StefanZott/SmartHomeSystemBasisStation/tmp/tasks/done/0047_pcb-layout-stromversorgung-leds.md

---
title: PCB-Layout — Stromversorgung und Status-LEDs platzieren und routen
created: 2026-09-24
jira: SHBS-21
priority: high
type: feature
status: done
---

## Kontext

Stromversorgung und Status-LEDs sind im Schaltplan fertig, im PCB aber erst
teilweise umgesetzt. Das Review vom 2026-09-24
([Report](../../report/2026-09-24_pcb-review-stromversorgung-leds.md))
ergab mehrere Befunde (B2–B5). Ethernet läuft separat unter SHBS-10.

## Ziel

Stromversorgung und LEDs vollständig platziert und geroutet, mit eigener
Netzklasse für die Versorgungsnetze. DRC im Bereich ohne Fehler.

## Schritte

- [x] Erste Platzierung und Routing durch Bediener (WIP-Stand)
- [x] Netzklasse `Power` (0,6 mm, Via 0,8/0,4) für VBUS, +5V, +3V3, GND, SW anlegen (B2)
- [x] Schaltknoten im Schaltplan mit lokalem Label `SW` benennen
- [x] Bediener: KiCad öffnen, im PCB-Editor F8 (Netz `Net-(D11-K)` → `/Stromversorgung/SW`)
- [x] ~~Versorgungsleitungen auf Netzklassenbreite aufweiten~~ → ausgelagert in Task 0048
- [x] Buck-Wandler kompakt um PS1 anordnen, Schaltknoten kurz halten (B3)
- [x] Bediener: PCB öffnen, `B` (Zonen füllen), Sichtprüfung Wandler, speichern
- [x] +3V3 zu U6.2 und zu den LED-Anoden routen (B4)
- [x] Bediener: `B` und speichern nach B4-Routing
- [x] ~~DRC-Restmeldungen an J_PWR1 ausschließen~~ → ausgelagert in Task 0048:: 2× `starved_thermal`
      (A1, rechtes S1), 2× Kantenabstand NPTH (A12, linkes S1) —
      Hersteller-Landepattern, Pads per Leiterbahn angebunden (aus SHBS-20)
- [x] `docs/project/power_supply.md` und `hardware.md` um Layout-Stand ergänzen
- [x] Commit

## Fortschritt

- 2026-09-24: Task angelegt. Bediener hat Stromversorgung und LEDs erstmals
  platziert und geroutet, Zonen gefüllt. DRC gesamt: 75 Meldungen, davon
  144 offene Verbindungen überwiegend außerhalb dieses Bereichs. Stand wird
  als WIP-Commit gesichert, damit SHBS-20 separat committet werden kann.
  Nächster Schritt: Netzklasse `Power` (Punkt 2 des Reviews).

- 2026-09-25: Label `SW` in `Stromversorgung.kicad_sch` auf der Leitung ab
  PS1.6 gesetzt (Netzliste: `/Stromversorgung/SW` = C15.2, D11.1, L1.2,
  PS1.6; ERC unverändert). Netzklasse `Power` mit fünf Mustern in
  `BasisStation.kicad_pro` angelegt. Muster per DRC-Probe in Kopie geprüft
  (Abstand testweise 5 mm): GND, +3V3, VBUS, +5V greifen, SW erst nach F8.
  `power_supply.md` ergänzt. Nächster Schritt: F8 durch Bediener, dann
  Leitungen aufweiten.

- 2026-09-26: Buck-Wandler per Skript in der `.kicad_pcb` umplatziert
  (KiCad geschlossen, Sicherung im Scratchpad). C13 (66/49,3), C15
  (63,3/53,5, 90°), D11 (60,2/50,5, 90°), L1 (60,2/58,8, 90°), C14
  (60,2/64,1, 90°), R17 (67,5/57,5, 90°), R18 (69,5/57,5, 90°). 53 alte
  Leiterbahnen/Vias entfernt (SW, BST, FB, +3V3 komplett, +5V und GND am
  Wandler), neu geroutet auf F.Cu: Power-Netze 0,6 mm, BST 0,3, FB 0,25,
  5 GND-Vias 0,8/0,4. SW-Leitung ca. 9,2 mm (vorher 40,7 mm). Referenztexte
  von PS1, C15, R18 versetzt. DRC per CLI: im Bereich keine Kupfer-,
  Courtyard- oder Silk-Befunde außer veralteter Zonenfüllung; offen nur
  +3V3 zu U6/U7 (B4, bekannt). Nächster Schritt: `B` durch Bediener, dann
  +3V3 verteilen (B4).
- 2026-09-26 (später): Bediener hat Zonen gefüllt und gespeichert. DRC:
  75 Meldungen, davon **keine** im Wandler-Bereich. Kupferbefunde nur noch
  außerhalb: J_PWR1 (bekannte Ausschlüsse), U1-Padabstände, GND-Stummel
  (21,8/90,3). Offen im Bereich nur +3V3 zu U6/U7 (B4).
- 2026-09-26 (B4): +3V3 per Skript geroutet (F.Cu, 0,6 mm). Hauptleitung
  R17-Knick (67,5/62,1) → y 62,1 bis x 111 → 45° → U6.2 (119,35/64,45).
  LED-Zweig ab (105/62,1) über U6 (y 58,1) bis x 150, senkrecht bis
  y 155, Sammelleitung y 157,5 mit Stichen zu D7/D10/D8/D9-Anoden. Erste
  Variante links an U6 vorbei (x 105) wieder verworfen, weil sie USB, EN
  und ETH-SPI auf F.Cu abgeschnitten hätte. DRC: +3V3 außerhalb Ethernet
  vollständig verbunden, Kupferbefunde nur gegen veraltete Zonenfüllung.
- 2026-09-26 (B4, nach `B`): DRC 75 Meldungen (Stand wie vor B4, keine
  neuen), offene Verbindungen 144 → 139. Keine Befunde an den neuen
  +3V3-Leitungen.
- 2026-09-26: Abschluss auf Wunsch des Bedieners. Aufweiten VBUS/+5V und
  DRC-Ausschlüsse J_PWR1 in Task
  [0048](../open/0048_pcb-power-leitungen-aufweiten-drc-ausschluesse.md)
  ausgelagert (gleiches Ticket SHBS-21, bleibt offen). `hardware.md` um
  Layout-Stand ergänzt. Task nach `done/` verschoben.

## Commits

- c2ccc4a (WIP) Erster Layout-Stand Stromversorgung und LEDs
- 53c2221 (WIP) Netzklasse Power, Label SW, Session-Übergabe tmp/memory.md
- 0c19f62 (WIP) Buck-Wandler kompakt um PS1 platziert und neu geroutet
- 895aab9 +3V3 zu U6 und LED-Anoden geroutet, Task abgeschlossen

## Offene Fragen

- Keine.
