StefanZott/SmartHomeSystemBasisStation/tmp/tasks/done/0004_shbs5-rj45-magnetics-schaltplan.md

---
status: done
priority: high
type: feature
created: 2026-09-17
jira: SHBS-5
parent_jira: SHBS-3
---

# RJ45-Buchse, Leitungsterminierung und Link-LEDs im Schaltplan

## Ziel

Buchsenseite der Ethernet-Sektion auf dem Blatt `Ethernet.kicad_sch`
ergänzen: RJ45 mit integrierten Magnetics, Terminierung, Schirmanbindung und
Link-/Activity-LEDs.

Setzt Tasks `0002` und `0003` voraus.

## Aufgaben

1. RJ45-Buchse (Typ aus Task `0002`) platzieren und differenzielle Paare
   `TXP`/`TXN` und `RXP`/`RXN` mit dem W5500 verbinden.
2. **Mittelanzapfungen** der Übertrager gemäss Datenblatt beschalten —
   üblicherweise über je einen Kondensator gegen GND oder gegen eine gefilterte
   Versorgung. Verbindlich ist das Applikationsbeispiel des Buchsen-Datenblatts
   in Kombination mit dem W5500-Referenzdesign.
   **Achtung (WIZnet-Referenz):** Sind die Mittelanzapfungen *innerhalb* des
   Übertragers bzw. der RJ45-Buchse bereits zusammengefasst, muss das
   Anpassnetzwerk der `RX±`-Seite (2 × 50 Ω) **galvanisch vom CT-Knoten
   (3,3 V) getrennt** werden. Vor dem Zeichnen im Datenblatt der gewählten
   Buchse prüfen, ob die CTs intern verbunden sind.
3. **Bob-Smith-Terminierung** auf der Leitungsseite: je 75 Ω von den vier
   ungenutzten Paaren bzw. den Mittelpunkten auf einen gemeinsamen Knoten,
   von dort über einen HV-Kondensator (mind. 2 kV) gegen Chassis-GND.
4. **Schirmanbindung:** Schirm der Buchse auf ein separates `CHASSIS`-Netz.
   Die Verbindung zu Signal-GND als **bestückbare Option** ausführen (0-Ω-Brücke
   plus paralleler HV-Kondensator), damit die Kopplung bei EMV-Problemen
   umkonfiguriert werden kann, ohne die Platine zu ändern.
5. **Link-/Activity-LEDs:** LED-Ausgänge des W5500 sind **active low** und
   treiben gegen GND. Vorwiderstände nach dem Muster der Status-LEDs
   dimensionieren (vgl. `R13`–`R16`, 220 Ω). Prüfen, ob die gewählte Buchse
   die LEDs bereits integriert — dann entfallen diskrete LEDs.
6. Referenzen fortlaufend zur bestehenden Nummerierung vergeben (aktuell
   höchste: `R26`, `D12`, `C15`, `J6`, `U6`).
7. ERC laufen lassen; auf dem `CHASSIS`-Netz ein `PWR_FLAG` setzen, sonst
   meldet KiCad ein nicht getriebenes Netz.

## Sollbeschaltung RJ45 (`T1`, Würth 7499011121A)

Der Bediener zeichnet in KiCad; der Agent prüft danach gegen die Netzliste.

**Die Buchse bringt Bob-Smith-Terminierung und den 2-kV-Kondensator bereits
mit** (4 × 75 Ω + 1 nF/2 kV, Datenblatt S. 2, an den Kabelkontakten 4, 5, 7 und 8 —
nicht zu verwechseln mit Schaltplan-Referenzen).
Extern ist dafür **nichts** zu bauen. Übertrager 1:1, 350 µH — deckt sich mit
der Forderung des W5500-Datenblatts (Abschnitt 5.5.5).

### Signalpaare

| Buchsen-Pin | Signal | Netz |
| --- | --- | ---- |
| 1 | `TD+` | `ETH_TXP` |
| 3 | `TD−` | `ETH_TXN` |
| 4 | `RD+` | `ETH_RXP` |
| 6 | `RD−` | `ETH_RXN` |

> **Fallstrick:** Eine Textextraktion des Datenblatt-Schaltbilds liefert die
> Reihenfolge `RD+, CRD, RD−, TD+, CTD, TD−` — **Sende- und Empfangspaar
> vertauscht**. Die obige Zuordnung wurde über die Koordinaten der
> Beschriftung im PDF geprüft und stimmt mit dem offiziellen Würth-Symbol
> überein.

### Mittelanzapfungen und MDI-Abschluss

Geklärt am 18.09.2026 aus dem WIZnet-Referenzschaltbild
(`pcb/Datasheets/wiznet_W5500_ref-schematic_RJ45-with-magnetics.pdf`).
Vollständiger Abgleich:
[tmp/report/2026-09-18_shbs-5-mdi-referenzabgleich.md](../../report/2026-09-18_shbs-5-mdi-referenzabgleich.md).

Die Sende- und Empfangszweige brauchen mehr als die blosse Paarverbindung.
Der Sendetreiber des W5500 arbeitet stromgesteuert und braucht eine
**gespeiste** Mittelanzapfung; der Empfänger arbeitet spannungsgesteuert,
bringt seine Vorspannung selbst mit und wird deshalb **gleichstromgetrennt**.

**Sendezweig**

| Bauteil | von | nach |
| --- | --- | ---- |
| 49,9 Ω 1 % | `+3V3A` | `U7.1` `TXN` |
| 49,9 Ω 1 % | `+3V3A` | `U7.2` `TXP` |
| 10 Ω 1 % | `+3V3A` | Knoten `TCT` |
| 22 nF | Knoten `TCT` | `GND` |
| — | Knoten `TCT` | `T1.2` `CTD` |

**Empfangszweig**

| Bauteil | von | nach |
| --- | --- | ---- |
| 6,8 nF | `U7.6` `RXP` | `T1.4` `RD+` — **in Serie**, ersetzt die direkte Verbindung |
| 6,8 nF | `U7.5` `RXN` | `T1.6` `RD−` — **in Serie**, ersetzt die direkte Verbindung |
| 49,9 Ω 1 % | `U7.6` `RXP` (chipseitig, vor dem Kondensator) | Knoten `RCT` |
| 49,9 Ω 1 % | `U7.5` `RXN` (chipseitig, vor dem Kondensator) | Knoten `RCT` |
| 10 nF | Knoten `RCT` | `GND` |
| — | Knoten `RCT` | `T1.5` `CRD` |

> **Achtung bei den 6,8 nF:** Sie liegen **in Serie** in den beiden
> Empfangsleitungen. Die bestehende Direktverbindung `U7.6`–`T1.4` und
> `U7.5`–`T1.6` wird dadurch aufgetrennt. Die 49,9 Ω hängen auf der
> **Chipseite** der Kondensatoren.

Warum das nicht optional ist: Ohne die Abschlusswiderstände stimmt die
Leitungsimpedanz nicht, ohne die Serienkondensatoren liegt der Gleichanteil
des Chips auf dem Übertrager. Beides zeigt weder ERC noch ein einfacher
Funktionstest — die Symptome sind sporadische Paketfehler und Abbrüche bei
längeren Kabeln.

### Getrennte Analogversorgung (entschieden 18.09.2026)

Digital- und Analogversorgung werden getrennt, **innerhalb von SHBS-5**.
Begründung: Späteres Nachrüsten hiesse, die sieben Abblockkondensatoren aus
Task 0003 ein zweites Mal umzuhängen. Der Buck-Zweig aus SHBS-4 ist nicht
betroffen — die Ferritperle sitzt auf dem Ethernet-Blatt.

**Neues Netz `+3V3A`**, gespeist aus `+3V3` über eine Ferritperle:

| Bauteil | von | nach | Hinweis |
| --- | --- | ---- | --- |
| Ferritperle `FB1` | `+3V3` | `+3V3A` | 100–2000 Ω bei 100 MHz, Dauerstrom ≥ 300 mA |
| `PWR_FLAG` | `+3V3A` | — | sonst meldet ERC das Netz als nicht getrieben |

**Umzuhängen von `+3V3` auf `+3V3A`:**

| Bisher auf `+3V3` | Neu |
| --- | --- |
| `U7.4`, `U7.8`, `U7.11`, `U7.15`, `U7.17`, `U7.21` (`AVDD`) samt `C17`–`C22` | `+3V3A` |
| `C27` 10 µF Stützkondensator | `+3V3A` |
| Abschlusswiderstände `TXP`/`TXN` (49,9 Ω, siehe oben) | `+3V3A` |
| Speisung `TCT` (10 Ω, siehe oben) | `+3V3A` |

**Bleibt auf `+3V3` (digital):**

| | |
| --- | --- |
| `U7.28` `VDD` samt `C16` | Digitalversorgung des Bausteins |
| `R28`–`R32` | Pull-ups an PMODE, `INTn`, `RSTn` |
| `R33`, `R34` | LED-Vorwiderstände |

Das entspricht der Aufteilung im Referenzschaltbild, wo `3V3D` den `VDD`-Pin
und die LEDs speist, während `3V3A` an allen `AVDD`-Pins und am Sendezweig
liegt.

**Hinweis:** Dieser Schritt ändert Bauteile, die in Task 0003 bereits gesetzt
wurden. Das ist beabsichtigt — Task 0003 bleibt abgeschlossen, die Änderung
läuft unter 0004, weil sie erst durch den Referenzabgleich entstanden ist.

### Schirm und unbenutzte Pins

| Buchsen-Pin | Beschaltung |
| --- | --- |
| `S1`, `S2` | Netz `CHASSIS` |
| 7, 8 | offen lassen, No-Connect-Flag |

Kopplung `CHASSIS` gegen `GND` als **bestückbare Option**: 0-Ω-Brücke parallel
zu einem HV-Kondensator (mind. 2 kV). So lässt sich das Verhalten bei
EMV-Problemen ohne Platinenänderung umkonfigurieren. `PWR_FLAG` auf `CHASSIS`
setzen, sonst meldet ERC ein nicht getriebenes Netz.

### Link- und Activity-LEDs

Die LEDs sitzen in der Buchse. Die LED-Ausgänge des W5500 sind **active low**
und ziehen gegen `GND` — die Anode liegt daher über den Vorwiderstand auf
`+3V3`.

| Buchsen-Pin | Funktion | Beschaltung |
| --- | --- | --- |
| 11 | LED grün, Anode | über **220 Ω** nach `+3V3` |
| 12 | LED grün, Kathode | `ETH_LINKLED` → W5500 Pin 25 |
| 9 | LED gelb, Anode | über **220 Ω** nach `+3V3` |
| 10 | LED gelb, Kathode | `ETH_ACTLED` → W5500 Pin 27 |

Dimensionierung: Flussspannung laut Würth-Datenblatt 1,8–2,4 V bei 20 mA. Bei
3,3 V und 220 Ω stellen sich rund **6 mA** ein — konsistent zu den
Status-LEDs `D7`–`D10` des Projekts, die ebenfalls 220 Ω verwenden.

| Bauart | Bauteil | Wert | Symbol | Footprint | Anzahl | Status |
| --- | --- | ---- | --- | --- | --- | --- |
| **Widerstand** | LED-Vorwiderstand | 220 Ω, 5 % | `Device:R` | `Resistor_SMD:R_0805_2012Metric` | 2 | `R33`, `R34` gesetzt |
| Kondensator | HV-Kopplung `CHASSIS`–`GND` | 1 nF, **≥ 2 kV** | `Device:C` | gehäuseabhängig, 1206 oder größer | 1 | `C28` gesetzt, Typ offen |
| **Widerstand** | Brücke `CHASSIS`–`GND` | 0 Ω, **DNP** | `Device:R` | `Resistor_SMD:R_0805_2012Metric` | 1 | `R35` gesetzt |
| **Widerstand** | Abschluss `TXP`/`TXN` | 49,9 Ω, **1 %** | `Device:R` | `Resistor_SMD:R_0805_2012Metric` | 2 | offen |
| **Widerstand** | Abschluss `RXP`/`RXN` | 49,9 Ω, **1 %** | `Device:R` | `Resistor_SMD:R_0805_2012Metric` | 2 | offen |
| **Widerstand** | Speisung `TCT` | 10 Ω, **1 %** | `Device:R` | `Resistor_SMD:R_0805_2012Metric` | 1 | offen |
| Kondensator | Abblockung `TCT` | 22 nF | `Device:C` | `Capacitor_SMD:C_0805_2012Metric` | 1 | offen |
| Kondensator | Serienkopplung `RXP`/`RXN` | 6,8 nF | `Device:C` | `Capacitor_SMD:C_0805_2012Metric` | 2 | offen |
| Kondensator | Abblockung `RCT` | 10 nF | `Device:C` | `Capacitor_SMD:C_0805_2012Metric` | 1 | offen |
| Ferritperle | `FB1` Trennung `+3V3`/`+3V3A` | 100–2000 Ω @ 100 MHz, ≥ 300 mA | `Device:FerriteBead` | `Inductor_SMD:L_0805_2012Metric` | 1 | offen, Typ wählen |

Die vier **49,9 Ω mit 1 %** sind toleranzkritisch — sie bilden zusammen die
100-Ω-Abschlussimpedanz der Ethernet-Leitung.

Der HV-Kondensator braucht wegen der Spannungsfestigkeit eine größere
Bauform als 0805 — Typ erst nach Auswahl festlegen.

## Ergebnis (18.09.2026)

Blatt `ethernet.kicad_sch` vollständig. **Alle 29 Pin-Prüfungen des W5500
bestanden**, 35 Bauteile, keine doppelten Referenzen. ERC: 0 Fehler,
7 Warnungen — alle sieben vorbestehend, das Ethernet-Blatt meldet nichts.

### MDI-Abschluss

| Ref | Wert | Funktion |
| --- | ---- | --- |
| `R36`, `R37` | 49,9 Ω 1 % | Abschluss `TXP`/`TXN` nach `+3V3A` |
| `R38` | 10 Ω 1 % | Speisung Mittelanzapfung `TCT` |
| `C32` | 22 nF | Abblockung `TCT` |
| `C29`, `C30` | 6,8 nF | **in Serie** in `RXP`/`RXN` |
| `R39`, `R40` | 49,9 Ω 1 % | Abschluss `RXP`/`RXN` auf `RCT` |
| `C31` | 10 nF | Abblockung `RCT` |

Die Mittelanzapfungen sind über die lokalen Labels `TCT` und `RCT` angebunden
statt über durchgezogene Leitungen — das vermeidet rund ein Dutzend
Leitungskreuzungen quer über das Blatt.

### Versorgungstrennung

| Netz | Liegt darauf |
| ---- | --- |
| `+3V3A` | `U7.4/8/11/15/17/21` mit `C17`–`C22`, Stütz `C27`, TX-Abschluss `R36`–`R38`, `PWR_FLAG` |
| `+3V3` | `U7.28` mit `C16`, Pull-ups `R28`–`R32`, LED-Vorwiderstände `R33`/`R34` |

Verbunden über `FB1`.

### Schirmung

`T1.S1`/`T1.S2` auf `CHASSIS`, gekoppelt über `C28` (1 nF/2 kV) nach `GND`,
`R35` mit 0 Ω als unbestückte Brücke parallel.

### Arbeitsteilung

Der Agent hat das Blatt diesmal selbst gezeichnet, nicht nur spezifiziert.
Ohne KiCad im Container war das nur über direkte Bearbeitung der
S-Expression möglich; die Prüfung erfolgte geometrisch über einen
Netz-Tracer, der Draht-Endpunkte, Pin-Positionen, Labels und T-Abzweige auf
Drahtmitten auswertet.

### Nacharbeit (kosmetisch, kein Funktionsmangel)

- **`FB1` trägt ein Widerstandssymbol.** Für `Device:FerriteBead` stand offline
  keine Symboldefinition zur Verfügung. Netzliste und Footprint
  (`Inductor_SMD:L_0805_2012Metric`) stimmen; in KiCad auf
  `Device:FerriteBead` umstellen. Hinweis als verstecktes Feld am Bauteil.
- **`+3V3A` ist ein lokales Label, kein Power-Symbol** — gleicher Grund.
  Funktioniert, sieht neben den `+3V3`-Symbolen aber uneinheitlich aus.
- **Platzierung ist funktional, nicht schön.** Alles liegt im freien Band bei
  y = 118–132 mit 7,62 mm Spaltenabstand. Einige Leitungen kreuzen ohne
  Verbindung; an allen echten Abzweigen sitzen geprüfte Knotenpunkte.
- **`C28` (1 nF/2 kV)** braucht noch einen konkreten Typ mit Bestellnummer.

## Akzeptanzkriterien

- [x] RJ45 im Schaltplan, alle acht Leitungspins und der Schirm beschaltet.
- [x] Differenzielle Paare zum W5500 vollständig, Netznamen sprechend.
- [x] Bob-Smith-Terminierung: entfällt, in der Würth-Buchse integriert.
- [x] Mittelanzapfungen nach Referenzschaltbild beschaltet (`TCT` gespeist,
      `RCT` gleichstromgetrennt).
- [x] MDI-Abschluss vollständig: 4 × 49,9 Ω 1 %, 2 × 6,8 nF in Serie,
      10 Ω 1 %, 22 nF, 10 nF.
- [x] Netz `+3V3A` angelegt, über Ferritperle aus `+3V3` gespeist, `PWR_FLAG`
      gesetzt; `AVDD`-Pins, deren Abblockung und der Sendezweig darauf umgehängt.
- [x] Schirmanbindung als bestückbare Option (0 Ω ‖ HV-C) ausgeführt.
- [x] Link-/Activity-Anzeige vorhanden (integriert oder diskret).
- [x] ERC ohne neue Fehler.

## Betroffene Dateien

- `pcb/BasisStation/Ethernet.kicad_sch`
- `pcb/BasisStation/ERC.rpt`
