StefanZott/SmartHomeSystemBasisStation/tmp/tasks/done/0024_logs-led-en-gb.md

---
status: done
priority: medium
type: refactor
created: 2026-06-02
jira: SHBS-2
---

# Log-Strings und LED-Enums en-GB

## Done-Kriterien

- [x] Keine deutschen Log/printf-Strings in `main/`
- [x] `LED_ON` / `LED_THRESHOLD` / `LED_OFF` statt `LED_EIN` usw.
