StefanZott/SmartHomeSystemBasisStation/docs/project/communication.md

---
status: active
last_updated: 2026-09-18
type: project-doc
---

# Kommunikation — SmartHomeSystemBasisStation

Logische Schnittstellen (WLAN, HTTP, SPIFFS) und Verweis auf physische Anbindung.

Verzahnte Projekte / Produktscope: [project-scope.md](../related-projects/project-scope.md).

Physische Schnittstellen (USB, PROG, JTAG, Ethernet): [hardware.md](hardware.md).

Ethernet-Architektur (W5500 über SPI, Begründung): [ethernet.md](ethernet.md).

## Persistente Konfiguration (SPIFFS)

| Pfad | Inhalt |
|---|---|
| `/spiffs/configuration.json` | WLAN: SSID, Passwort, Kanal, RSSI, Auth-Modus, IP, Netmask, Gateway (Felder als JSON; siehe `main.c` / `WLAN.c`) |

Schreibzugriff erfolgt über `file_writeContentInFile()` (`FileManagement`).

## WLAN

- **SoftAP** für Ersteinrichtung / Konfiguration (u. a. festes AP-Passwort und Kanal in `WLAN.c` — siehe Quellcode `AP_ESP_WIFI_*`).
- **Station** für Betrieb im Heimnetz; Parameter aus `configuration.json` und Kconfig (`CONFIG_ESP_WIFI_*`).

## HTTP-Server (`WebServer.c`)

Basis: `esp_http_server`, u. a. Wildcard-Match für statische Dateien unter `/*`.

### Registrierte URI-Beispiele (Auszug)

Konfiguration und Diagnose (GET/POST je nach Handler im Quellcode):

- `/getConnectionInfo`, `/getWifiState`, `/disconnectWIFIHandler`
- `/getInfos`, `/FWversion`
- `/getSsidList`, `/newSSID`
- `/ledTest`, `/ledSingleTest`
- `/alexaTest`
- Statische UI: `/html/*.html`, `/css/*`, `/js/*`, `/img/*`, `/favicon.ico`

Für verbindliche Methoden (GET vs. POST) und Request-Bodies die Implementierung in `WebServer.c` heranziehen.

## Web-Assets

- Laufzeit: primär aus SPIFFS-Pfad `/spiffs` (vgl. `startWebServer`).
- Quell-Assets: Verzeichnis `spiffs/` im Repository.
- Zusätzlich: `EMBED_FILES` in `main/CMakeLists.txt` für eingebettete Ressourcen.

## Serielle Konsole / Flash

Typisch über USB-UART bzw. JTAG-Adapter — ESP-IDF-Standardfluss (`idf.py flash monitor`). Siehe [architecture.md](architecture.md) (Deployment).

## Abgrenzung

- Kein separates API-Schema (OpenAPI) im Repository; diese Datei ist die Einstiegsübersicht.
- **Ethernet:** nicht in der aktuellen Firmware-Kommunikationsschicht vorhanden
  (**SHBS-11**). Der Schaltplan ist fertig (SHBS-5), das Layout ebenfalls
  (SHBS-10, 2026-09-29).
  Angebunden über **WIZnet W5500** am SPI-Bus; ESP-IDF betreibt ihn im
  MACRAW-Modus unter lwIP, aus Sicht der Kommunikationsschicht also ein
  reguläres `esp_netif`-Interface neben WLAN. Erwarteter Durchsatz
  **15–20 Mbit/s** — begrenzt durch den SPI-Bus, nicht durch die Leitung.
  Details: [ethernet.md](ethernet.md).
- **Koexistenz WLAN/Ethernet** ist noch nicht entworfen: `WLAN.c` und
  `WebServer.c` kennen bisher genau ein Netif. Interface-Priorität,
  Fallback-Verhalten und SoftAP-Verhalten bei bestehendem Ethernet-Link sind in
  SHBS-11 zu klären.
