StefanZott/SmartHomeSystemBasisStation/tmp/tasks/done/0011_clang-format-tidy-einfuehren.md

---
status: done
priority: medium
type: feature
created: 2026-06-02
completed: 2026-06-02
phase: C
jira: SHBS-1
skipped: true
---

# `.clang-format` und `.clang-tidy` einführen

## Status

**Übersprungen** auf Anweisung des Bedieners (2026-06-02). Keine Umsetzung, kein Commit.

Task kann bei Bedarf erneut als neuer Task oder Reopen angelegt werden.

## Ursprüngliches Ziel

Code-Style- und Linting-Tools für C/C++ gemäß AGENTS.md §5 im Repository verankern.

## Done-Kriterien

- [ ] `.clang-format` und `.clang-tidy` existieren im Root. _(übersprungen)_
- [ ] Konfiguration ist dokumentiert. _(übersprungen)_
- [ ] Build bleibt erfolgreich. _(n/a)_

## Referenz

[docs/project/struktur-anpassung-agents.md](../../../docs/project/struktur-anpassung-agents.md) — Abschnitt 8.2
