StefanZott/SmartHomeSystemBasisStation/tmp/tasks/done/0021_git-altlasten-entfernen.md

---
status: done
priority: high
type: chore
created: 2026-06-02
jira: SHBS-2
---

# Git-Altlasten entfernen

## Done-Kriterien

- [x] `BasisStation_old.pdf` und `prompt.txt` aus dem Repository entfernt
- [x] Commit unter SHBS-2 (`42ac756`)
