StefanZott/SmartHomeSystemBasisStation/tmp/tasks/done/0025_clang-format-tidy.md

---
status: done
priority: medium
type: chore
created: 2026-06-02
jira: SHBS-2
---

# clang-format und clang-tidy einführen

## Done-Kriterien

- [x] `.clang-format` und `.clang-tidy` im Root
- [x] Kurzhinweis in `architecture.md` oder `tests/README.md`
