StefanZott/SmartHomeSystemBasisStation/tmp/tasks/done/0027_releases-secrets-readme.md

---
status: done
priority: low
type: docs
created: 2026-06-02
jira: SHBS-2
---

# releases.md und secrets-README pflegen

## Done-Kriterien

- [x] Veraltete Punkte in `releases.md` bereinigt
- [x] `secrets/README.md` mit Hinweis angelegt
