StefanZott/SmartHomeSystemBasisStation/pcb/Screenshot 2025-02-16 231649.png

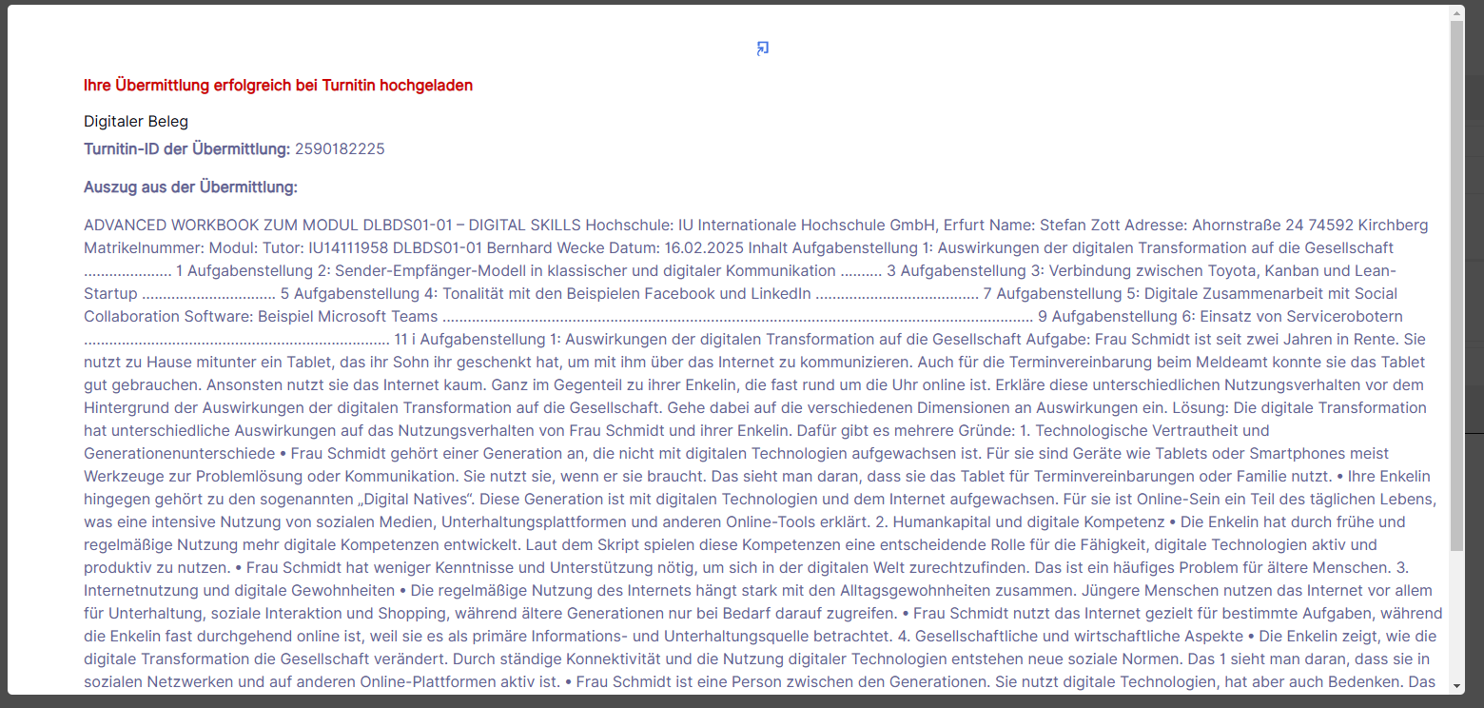
pcb/Screenshot 2025-02-16 231649.png
