StefanZott/SmartHomeSystemBasisStation/tmp/report/2026-09-29_s2-liegend.png

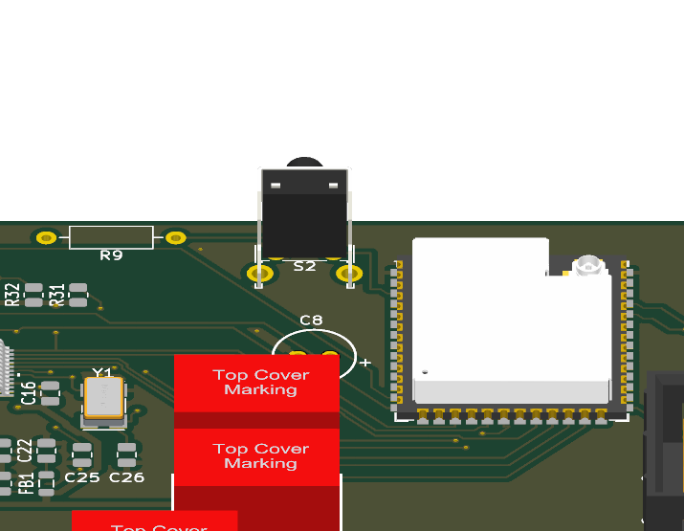
tmp/report/2026-09-29_s2-liegend.png
