StefanZott/SmartHomeSystemBasisStation/tmp/report/2026-09-30_layout-top-shbs42.png

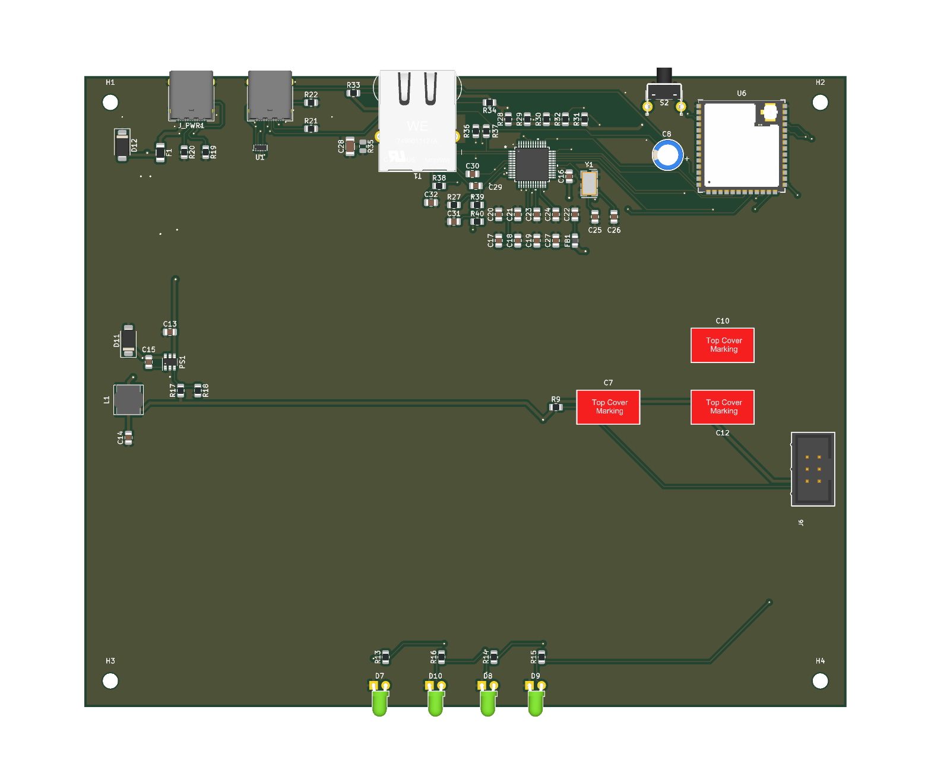
tmp/report/2026-09-30_layout-top-shbs42.png
