StefanZott/SmartHomeSystemBasisStation/tmp/sch_restore.kicad_sch

## KiCad design tmp/sch_restore.kicad_sch (2026-09-08)

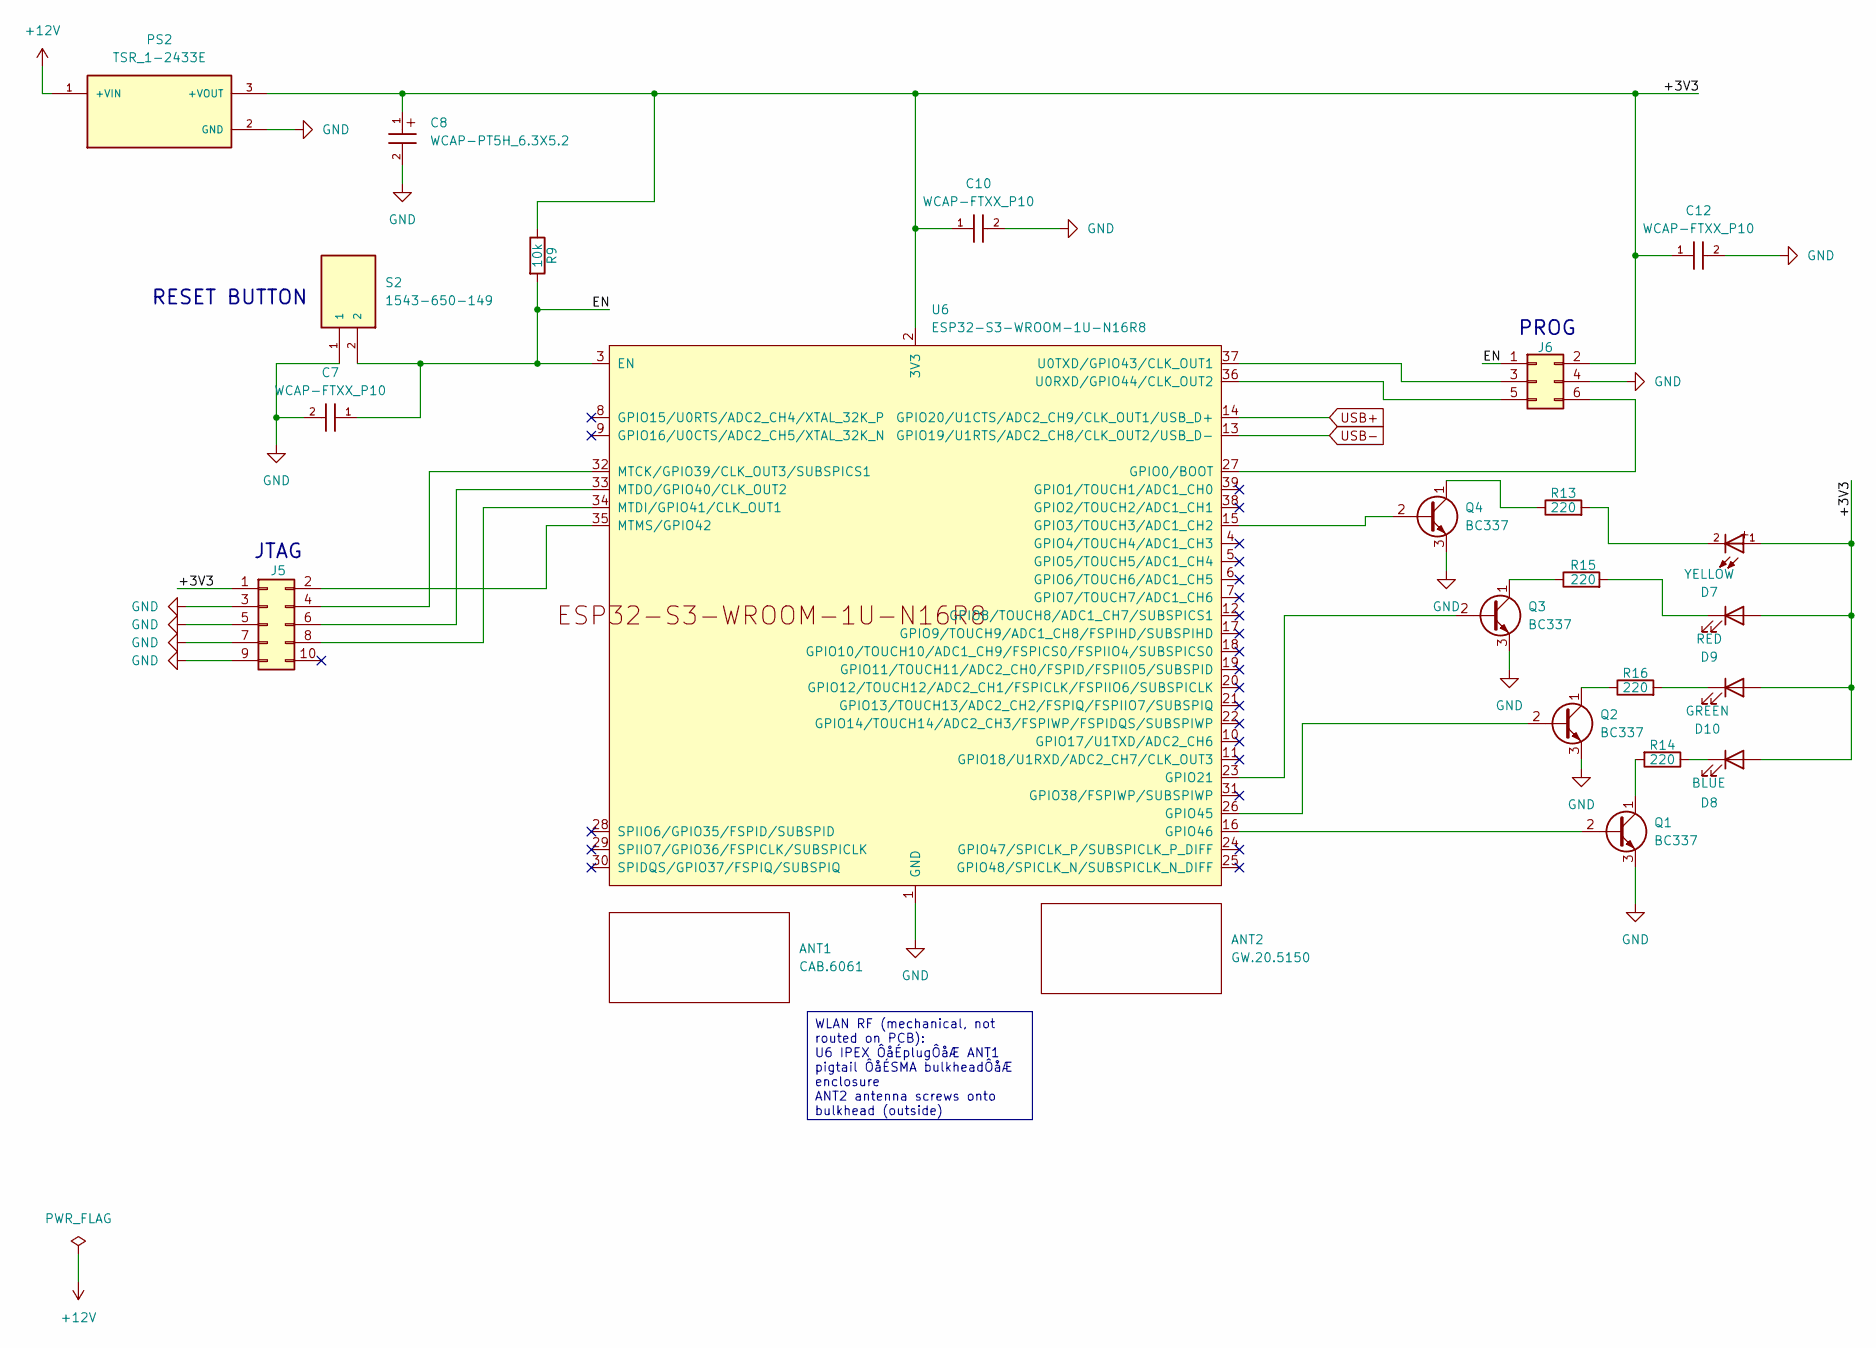
[picture p34: schematic sch_restore.kicad_sch]

Parts:
ANT1: CAB.6061; Manufacturer_Part_Number CAB.6061; Mouser Part Number 742-CAB.6061
ANT2: GW.20.5150; Manufacturer_Part_Number GW.20.5150; Mouser Part Number 742-GW.20.5150
C7, C10, C12: WCAP-FTXX_P10; WCAP-FTXX_P10L13W7H13
C8: WCAP-PT5H_6.3X5.2; WCAP-PT5H_6.3X5.2_DXL_
D7: YELLOW; WL-TMRC_3MM
D8: BLUE; WL-TMRW_3MM
D9: RED; WL-TMRW_3MM
D10: GREEN; WL-TMRC_3MM
J5: Conn_02x05_Odd_Even; 61201021621
J6: Conn_02x03_Odd_Even; 61200621621
PS2: TSR_1-2433E; CONV_TSR_1-2433E; PARTREV May 25, 2020
Q1, Q2, Q3, Q4: BC337; TO-92_Inline
R9: 10k; R_Axial_DIN0207_L6.3mm_D2.5mm_P10.16mm_Horizontal
R13, R14, R15, R16: 220; R_Axial_DIN0617_L17.0mm_D6.0mm_P20.32mm_Horizontal
S2: 1543-650-149; 1543650149; MOUSER_PART_NUMBER 652-1543-650-149
U6: ESP32-S3-WROOM-1U-N16R8; ESP32-S3-WROOM-1U; Mouser Part Number 356-ESP32S3WM1UN16R8

Connections:
+3V3: C8.1, C10.1, C12.1, D7.1, D8.2 (A), D9.2 (A), D10.2 (A), J5.1, J6.2, PS2.3 (+VOUT), R9.1, U6.2 (3V3)
+12V: PS2.1 (+VIN)
EN: C7.1, J6.1, R9.2, S2.2, U6.3 (EN)
GND: C7.2, C8.2, C10.2, C12.2, J5.3, J5.5, J5.7, J5.9, J6.4, PS2.2 (GND), Q1.3 (E), Q2.3 (E), Q3.3 (E), Q4.3 (E), S2.1, U6.1 (GND), U6.40 (GND), U6.41 (EPAD)
unnamed: D7.2, R13.2
unnamed: D8.1 (K), R14.1
unnamed: D9.1 (K), R15.2
unnamed: D10.1 (K), R16.2
unnamed: J5.2, U6.35 (MTMS/GPIO42)
unnamed: J5.4, U6.32 (MTCK/GPIO39/CLK_OUT3/SUBSPICS1)
unnamed: J5.6, U6.33 (MTDO/GPIO40/CLK_OUT2)
unnamed: J5.8, U6.34 (MTDI/GPIO41/CLK_OUT1)
unnamed: J6.3, U6.37 (U0TXD/GPIO43/CLK_OUT1)
unnamed: J6.5, U6.36 (U0RXD/GPIO44/CLK_OUT2)
unnamed: J6.6, U6.27 (GPIO0/BOOT)
unnamed: Q1.1 (C), R14.2
unnamed: Q1.2 (B), U6.16 (GPIO46)
unnamed: Q2.1 (C), R16.1
unnamed: Q2.2 (B), U6.26 (GPIO45)
unnamed: Q3.1 (C), R15.1
unnamed: Q3.2 (B), U6.23 (GPIO21)
unnamed: Q4.1 (C), R13.1
unnamed: Q4.2 (B), U6.15 (GPIO3/TOUCH3/ADC1_CH2)
USB+: U6.14 (GPIO20/U1CTS/ADC2_CH9/CLK_OUT1/USB_D+)
USB-: U6.13 (GPIO19/U1RTS/ADC2_CH8/CLK_OUT2/USB_D-)

Notes on the sheet:
RESET BUTTON
PROG
JTAG
WLAN RF (mechanical, not routed on PCB): U6 IPEX ÔåÉplugÔåÆ ANT1 pigtail ÔåÉSMA bulkheadÔåÆ enclosure ANT2 antenna screws onto bulkhead (outside)
