StefanZott/SmartHomeSystemBasisStation/main/LED.h

/*
*   LED.h
*
*   Created on: 28.12.2023
*   Author: Stefan Zott
*   
*   Description:
*   Configuration and control of the status LEDs.
*/

#ifndef LED_H_
#define LED_H_

#include "driver/ledc.h"

#define LED_BLUE                LEDC_CHANNEL_0
#define LED_YELLOW              LEDC_CHANNEL_1
#define LED_GREEN               LEDC_CHANNEL_2
#define LED_RED                 LEDC_CHANNEL_3
#define LED_MAX                 4

#define LED_GPIO_BLUE           GPIO_NUM_46
#define LED_GPIO_YELLOW         GPIO_NUM_3
#define LED_GPIO_GREEN          GPIO_NUM_45
#define LED_GPIO_RED            GPIO_NUM_21

#define ON                      (4096) // Set duty to 50%. (2 ** 13) * 50% = 4096
#define OFF                     (0) // Set duty to 0%. (2 ** 13) * 0% = 0
// #define BLINK                   "blink"
// #define NORMAL                  "normal"
// #define TEST                    "test"
// #define SINGLETEST              "singleTest"

#define BLINK_INTERVALL         1000
#define BLINK_FREQ              200

#define LEDC_TIMER              LEDC_TIMER_0
#define LEDC_MODE               LEDC_LOW_SPEED_MODE
// #define LEDC_CHANNEL_BLUE       LEDC_CHANNEL_0
// #define LEDC_CHANNEL_YELLOW     LEDC_CHANNEL_1
// #define LEDC_CHANNEL_GREEN      LEDC_CHANNEL_2
// #define LEDC_CHANNEL_RED        LEDC_CHANNEL_3
#define LEDC_DUTY_RES           LEDC_TIMER_13_BIT // Set duty resolution to 13 bits
// #define LEDC_DUTY_ON            (4096) // Set duty to 50%. (2 ** 13) * 50% = 4096
// #define LEDC_DUTY_OFF           (0) // Set duty to 0%. (2 ** 13) * 0% = 0
#define LEDC_FREQUENCY          (4000) // Frequency in Hertz. Set frequency at 4 kHz

typedef enum mode{
   NORMAL,
   BLINK,
   TEST,
   SINGLETEST,
   IDLE
} ledMode_t;

typedef struct ledState_t {
   int led;     // Which LED will be changed
   int state;   // ON - OFF
   ledMode_t mode;    // TEST - NORMAL - BLINK(Only for the blue LED) - SINGLETEST
} ledStateMessage;

typedef struct ledProfil_t {
   int state;   // ON - OFF
   ledMode_t mode;    // TEST - NORMAL - BLINK(Only for the blue LED) - SINGLETEST
} ledProfil;

extern QueueHandle_t xLedStateQueue;

void ledControlTask( void *pvParameters );

#endif /* LED_H_ */
